rtitmuss/torn/case/HiPro Case/img/IMG_9087.jpg

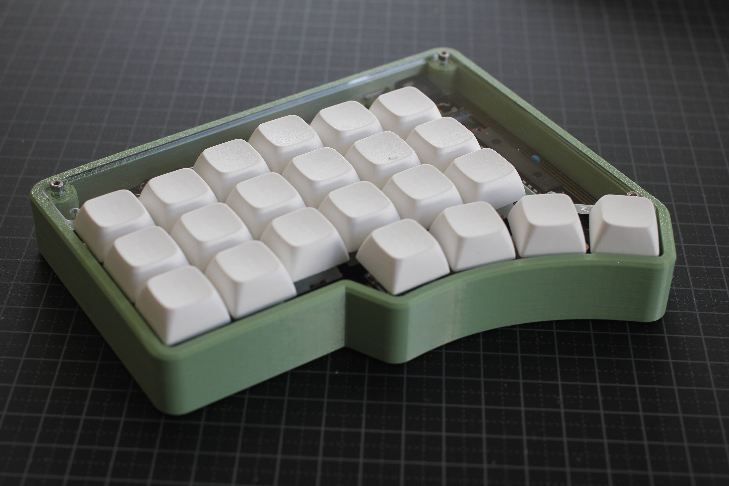
case/HiPro Case/img/IMG_9087.jpg
