rtitmuss/torn/case/HiPro Case/img/IMG_9090.jpg

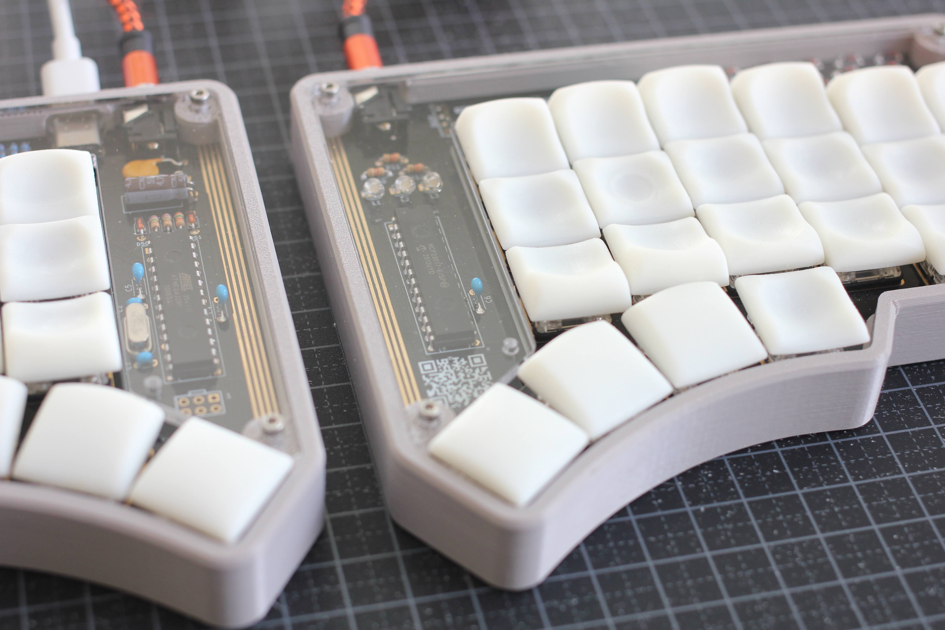
case/HiPro Case/img/IMG_9090.jpg
