rtitmuss/torn/case/Travel Case/img/PXL_20210807_115049295.jpg

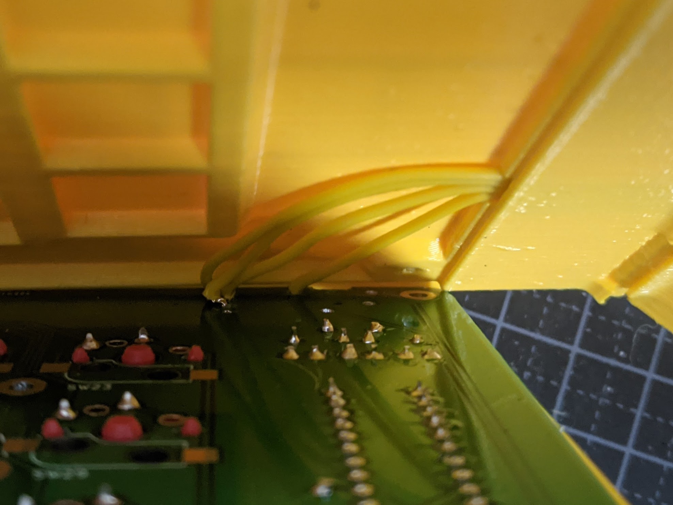
case/Travel Case/img/PXL_20210807_115049295.jpg
