rtitmuss/torn/case/Travel Case/img/PXL_20210807_120448581.jpg

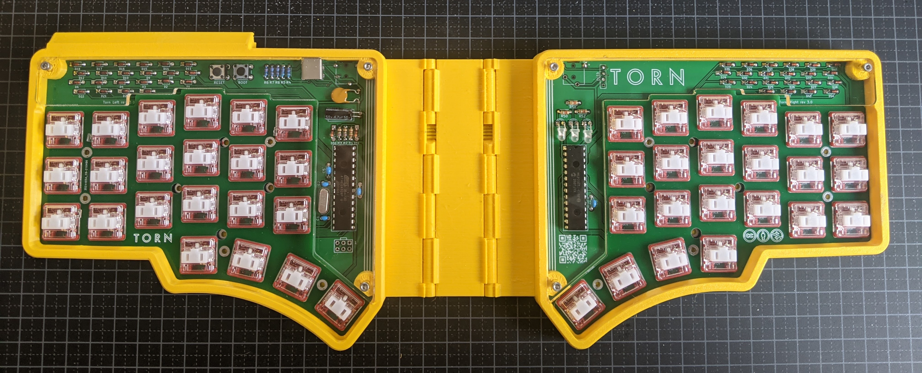
case/Travel Case/img/PXL_20210807_120448581.jpg
